corrados/edrumulus/hardware/prototype_3hhh/ltspice/edrumulus.asc

C1: cap; 15n
C2: cap; {Cp}
D1: schottky; BAT54
D2: schottky; BAT54
R1: res; {Rp}
R2: res; {Rp}
R3: res; {Rs}
V1: voltage; SINE(0 {Vp} 2k)
V2: voltage; 3.3
Named nets: 0
Piezo
gpio
gain adjustment
.tran 0 5m 2m
.param Rp 10k
.param Cp 1p
.param Vp 1
.step param Rs list 1k 2k 5k 10k
Rs needs min 10k for low current (1mA at 10V piezo input)
to make the forward voltage of the Shottky
diodes small (~0,3V) as the Teensy
GPIO input only supports -0,3V to 3,6V
If a pad draw current from the voltage divider, Rp+Rs cannot
be too large (~30k) as the 1.65V of the voltage divider will
otherwise drop. :(
Test your pads by reading from the analog pin when connected
vs disconnected (both should be around 1.65V)!
