corrados/edrumulus/hardware/prototype_3hhh/ltspice/edrumulus_hihat.asc

D1: diode; 1N4148
D2: diode; 1N4148
R1: res; {Rp}
R3: res; {Rs}
Rh1: res; {Rh1}
Rh2: res; {Rh2}
V2: voltage; 3.3
Named nets: 0
gpio
.tran 0 4m
.param Rp 10k
.param Rs 10k
Hihat Controller Potentiometer
.param Rh1 = Rh*P/100
.param Rh2 = Rh*(1-P/100)
.param Rh 35k
.step param P 1 99 10
choosing Rp ~ 1/2 Rh seems to be a good idea
too high Rp impacts maximum signal range
too low Rp impacts minimum signal range
